Chen-Jihang/Mini-Monitor/04_Images/photograph/IMG_3699.JPG

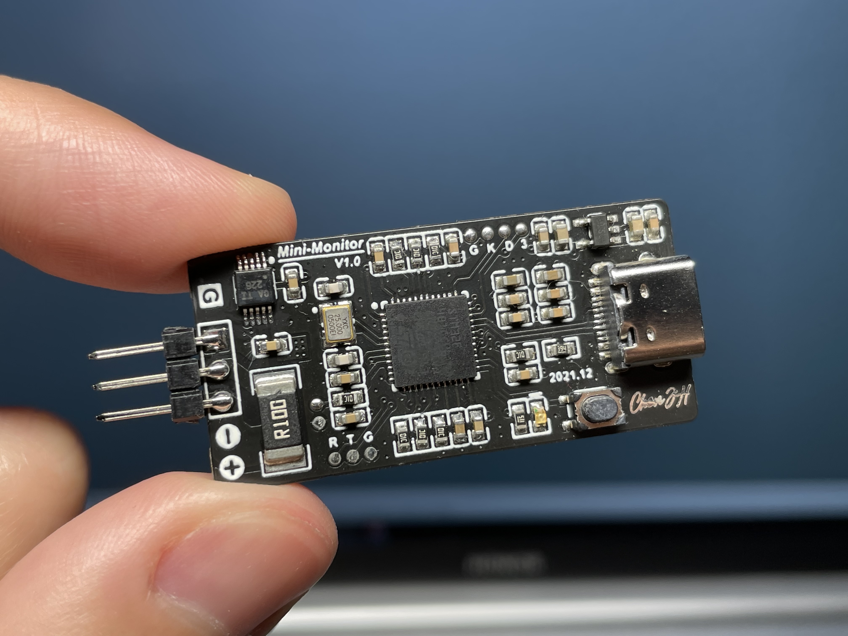
04_Images/photograph/IMG_3699.JPG
