Chen-Jihang/Mini-Monitor/04_Images/photograph/IMG_3701.JPG

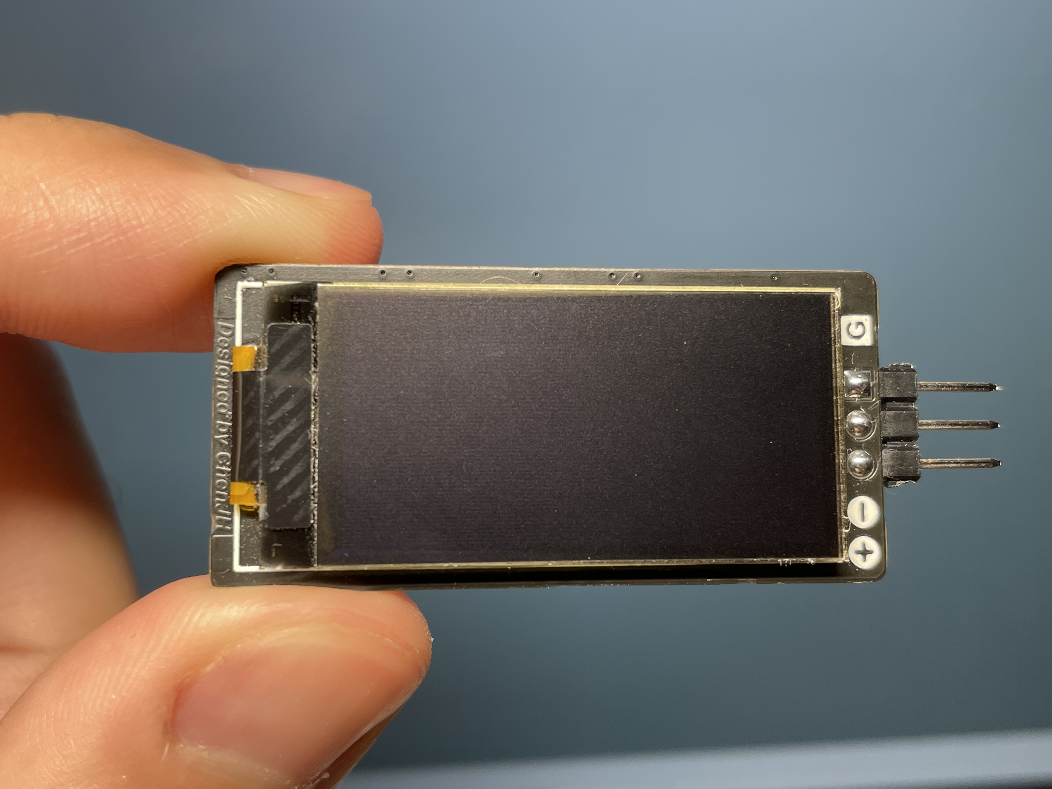
04_Images/photograph/IMG_3701.JPG
