Chen-Jihang/Mini-Monitor/04_Images/photograph/IMG_3709.JPG

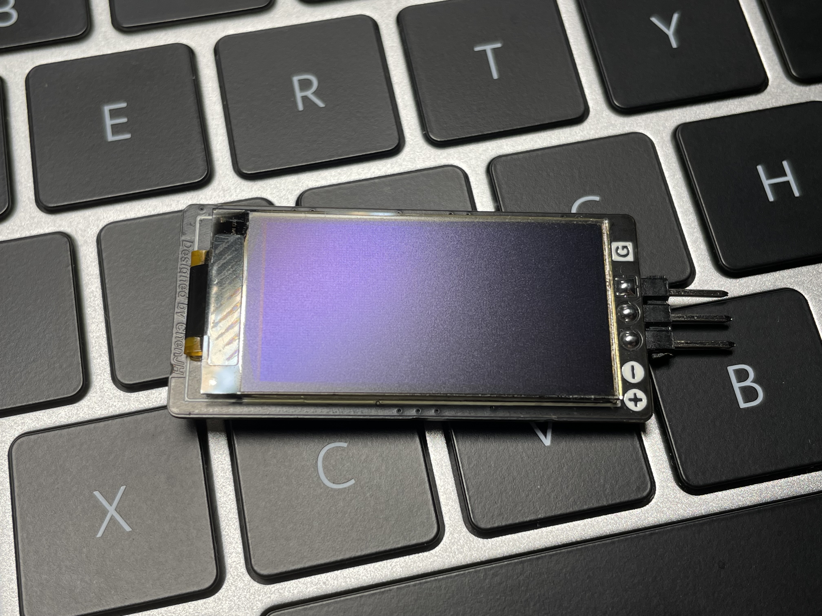
04_Images/photograph/IMG_3709.JPG
