Chen-Jihang/Mini-Monitor/04_Images/photograph/IMG_3772.JPG

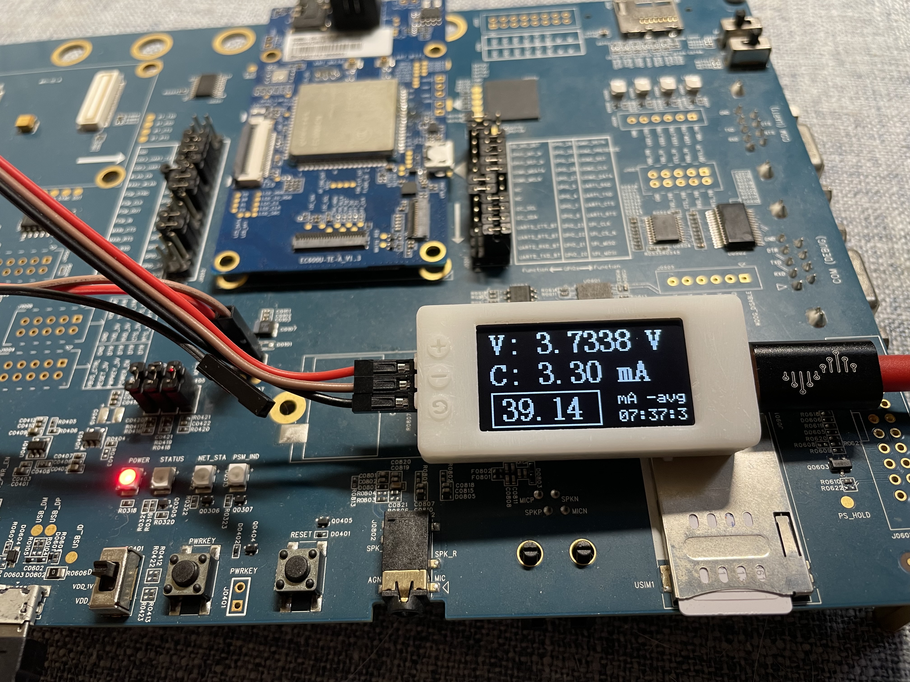
04_Images/photograph/IMG_3772.JPG
