Chen-Jihang/Mini-Monitor/04_Images/photograph/IMG_3781.JPG

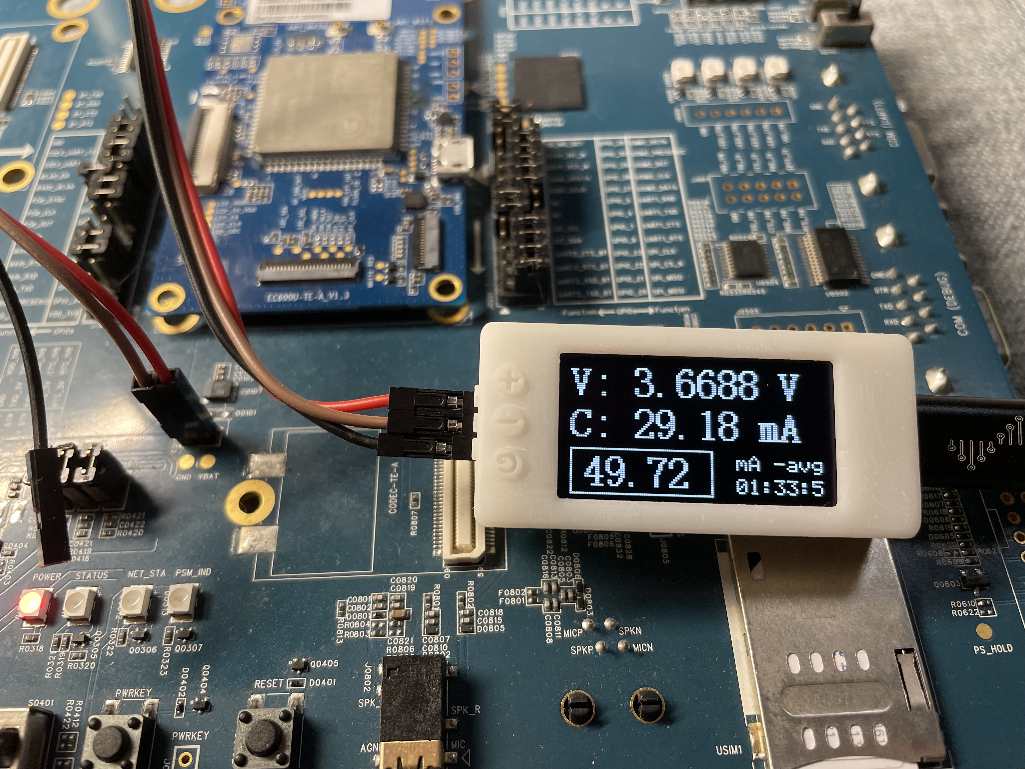
04_Images/photograph/IMG_3781.JPG
