Chen-Jihang/Mini-Monitor/04_Images/photograph/IMG_3813.JPG

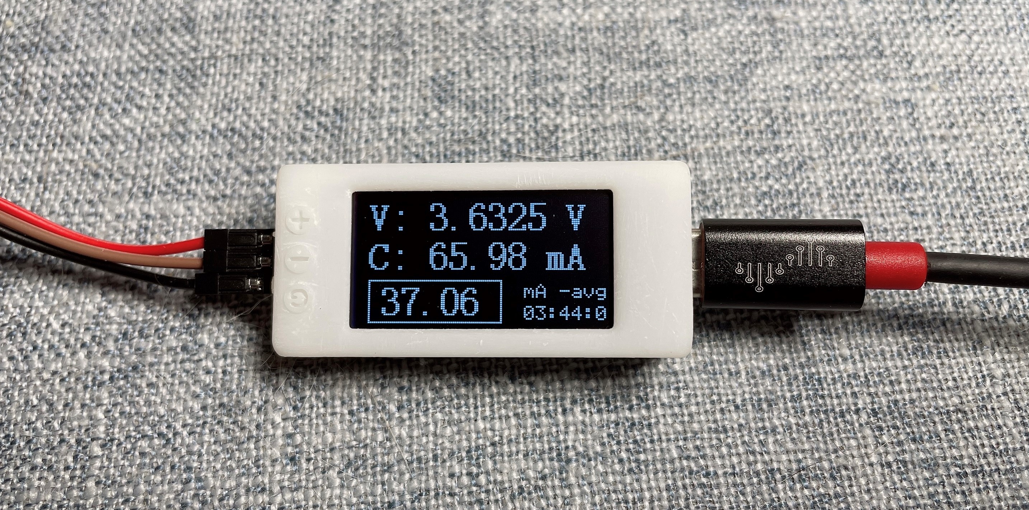
04_Images/photograph/IMG_3813.JPG
