Chen-Jihang/Mini-Monitor/04_Images/rendergraph/GEN_1.JPG

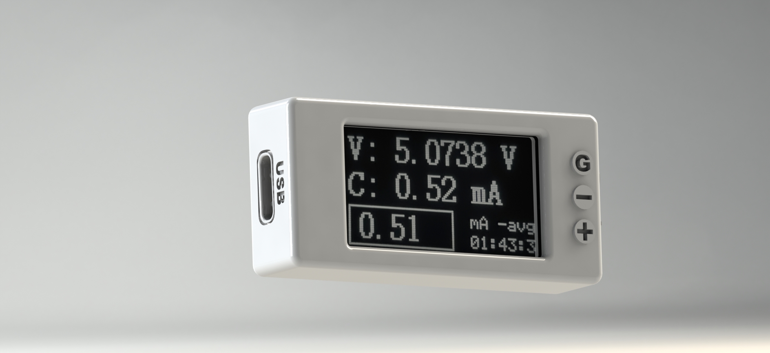
04_Images/rendergraph/GEN_1.JPG
