Chen-Jihang/Mini-Monitor/04_Images/rendergraph/GEN_3.JPG

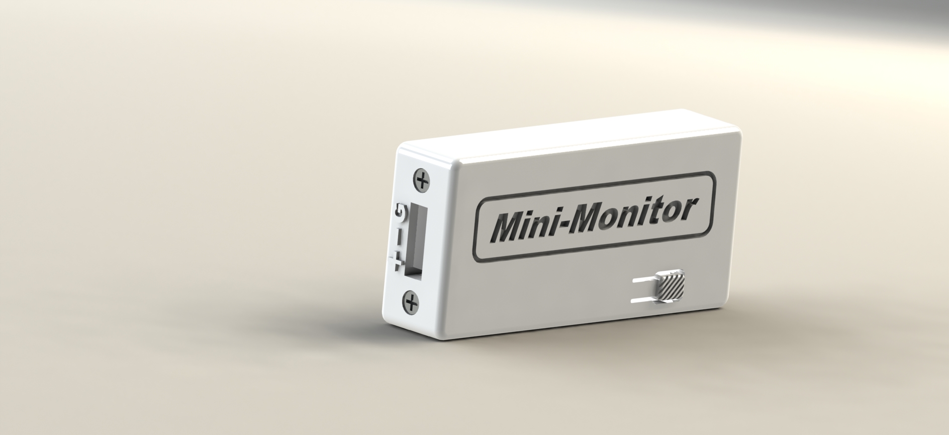
04_Images/rendergraph/GEN_3.JPG
