Chen-Jihang/Mini-Monitor/04_Images/rendergraph/GEN_6.JPG

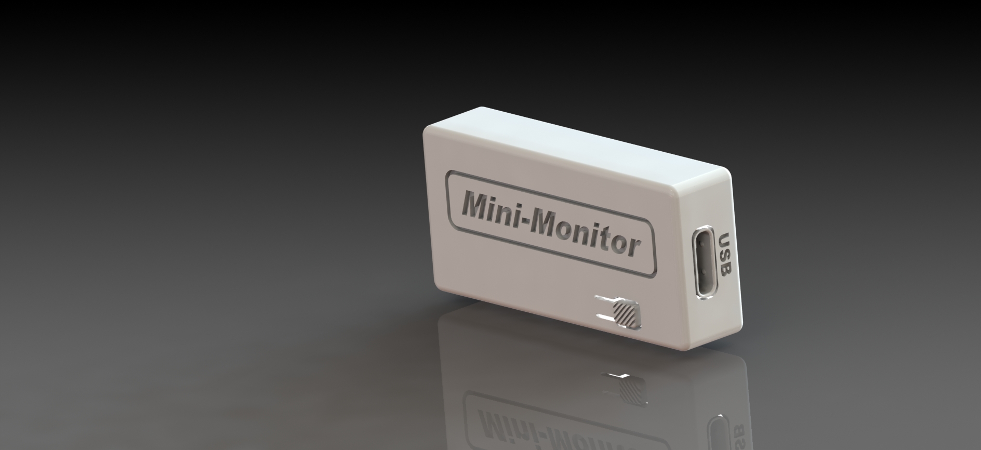
04_Images/rendergraph/GEN_6.JPG
