Chen-Jihang/Mini-Monitor/04_Images/rendergraph/GEN_9.JPG

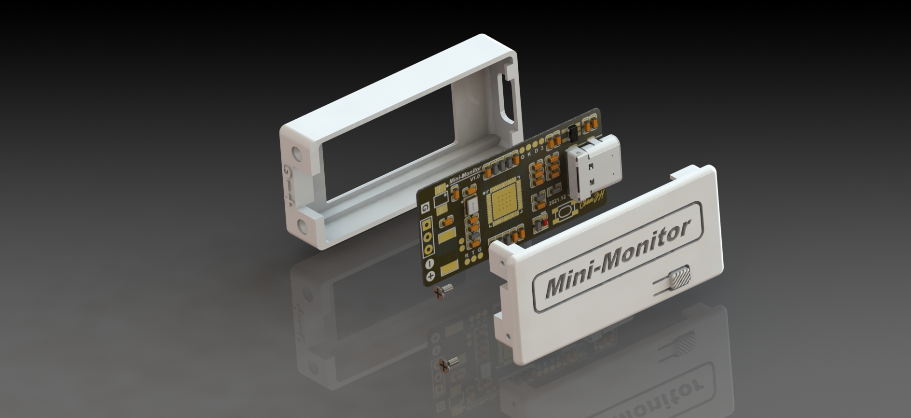
04_Images/rendergraph/GEN_9.JPG
