Chen-Jihang/Mini-Monitor/04_Images/rendergraph/GEN_11.JPG

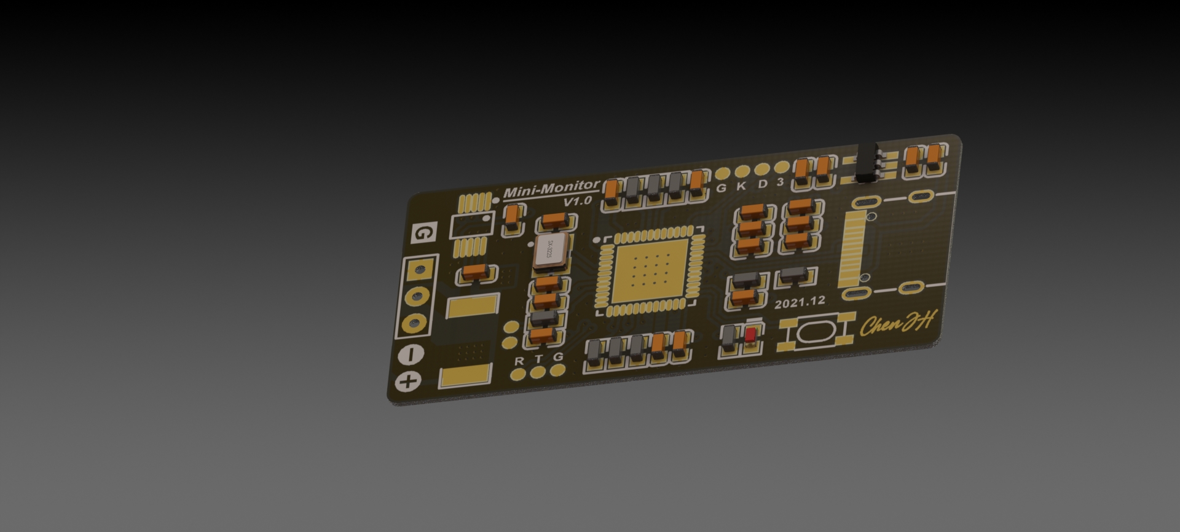
04_Images/rendergraph/GEN_11.JPG
