Chen-Jihang/Mini-Monitor/01_Software/Mini-Monitor__no_lvgl/HARDWARE/OLED/bmp.h

#ifndef __BMP_H
#define __BMP_H
//unsigned char BMP1[] =
//{
//	0x00,0x00,0x00,0x00,0x00,0x00,0x00,0x00,0x00,0x00,0x00,0x00,0x00,0x00,0x00,0x00,
//	0x00,0x00,0x00,0x00,0x00,0x00,0x00,0x00,0x00,0x00,0x00,0x00,0x00,0x00,0x00,0x00,
//	0x00,0x00,0x00,0x00,0x00,0x00,0x00,0x00,0x00,0x00,0x00,0x00,0x00,0x00,0x00,0x00,
//	0x00,0x00,0x00,0x00,0x00,0x00,0x00,0x00,0x00,0x00,0x00,0x00,0x00,0x00,0x00,0x00,
//	0x00,0x00,0x00,0x00,0x00,0x00,0x00,0x00,0x00,0x00,0x00,0x00,0x00,0x00,0x00,0x00,
//	0x00,0x00,0x00,0x00,0x00,0x00,0x00,0x00,0x00,0x00,0x00,0x00,0x00,0x00,0x00,0x00,
//	0x00,0x00,0x00,0x00,0x00,0x00,0x00,0x00,0x00,0x00,0x00,0x00,0x00,0x00,0x00,0x00,
//	0x00,0x00,0x00,0x00,0x00,0x00,0x00,0x00,0x00,0x00,0x00,0x00,0x00,0x00,0x00,0x00,
//	0x00,0x00,0x00,0x00,0x00,0x00,0x00,0x00,0x00,0x00,0x00,0x00,0x00,0xE0,0xE0,0x00,
//	0x00,0x00,0x80,0xE0,0xE0,0x00,0x00,0x00,0x80,0x80,0x80,0x00,0xC0,0xC0,0x80,0x00,
//	0x00,0x00,0xC0,0xC0,0xC0,0x00,0x80,0x80,0x80,0x00,0x00,0x00,0x00,0x00,0x00,0x00,
//	0x00,0x00,0x00,0x00,0x80,0xE0,0xE0,0x00,0x00,0x00,0x80,0xE0,0xE0,0x00,0x00,0x00,
//	0xC0,0xE0,0xE0,0xF0,0xF0,0xF0,0xE0,0xC0,0x00,0x00,0xE0,0xE0,0xC0,0x00,0x00,0x00,
//	0xE0,0xE0,0xE0,0x00,0x00,0xC0,0xC0,0xC0,0x00,0xE0,0xE0,0xE0,0xE0,0xE0,0xE0,0xE0,
//	0xE0,0xE0,0x00,0x80,0xC0,0xE0,0xF0,0x70,0x70,0xF0,0xE0,0xC0,0x00,0x00,0xC0,0xC0,
//	0xC0,0xC0,0xC0,0xC0,0xC0,0x80,0x00,0x00,0x00,0x00,0x00,0x00,0x00,0x00,0x00,0x00,
//	0x00,0x00,0x00,0x00,0x00,0x00,0x00,0x00,0x00,0x00,0x80,0xF0,0xFF,0xFF,0x3F,0xFF,
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
	0x00,0x00,0x00,0x00,0x00,0x0F,0x0F,0x0F,0x00,0x00,0x01,0x0F,0x0F,0x0F,0x01,0x00,
	0x00,0x0F,0x0F,0x0F,0x00,0x01,0x07,0x07,0x0F,0x0E,0x0E,0x0F,0x07,0x07,0x01,0x00,
	0x0F,0x0F,0x0F,0x00,0x00,0x00,0x0F,0x0F,0x0F,0x00,0x0F,0x0F,0x0F,0x00,0x00,0x07,
	0x0F,0x0F,0x0E,0x0E,0x00,0x01,0x07,0x07,0x0F,0x0E,0x0E,0x0F,0x07,0x07,0x01,0x00,
	0x0F,0x0F,0x0F,0x00,0x00,0x00,0x00,0x00,0x00,0x00,0x00,0x00,0x00,0x00,0x00,0x00,
	0x00,0x00,0x00,0x00,0x00,0x00,0x00,0x00,0x00,0x00,0x00,0x00,0x00,0x00,0x00,0x00,
	0x00,0x00,0x00,0x00,0x00,0x00,0x00,0x00,0x00,0x00,0x00,0x00,0x00,0x00,0x00,0x00,
	0x00,0x00,0x00,0x00,0x00,0x00,0x00,0x00,0x00,0x00,0x00,0x00,0x00,0x00,0x00,0x00,
	0x00,0x00,0x00,0x00,0x00,0x00,0x00,0x00,0x00,0x00,0x00,0x00,0x00,0x00,0x00,0x00,
	0x00,0x00,0x00,0x00,0x00,0x00,0x00,0x00,0x00,0x00,0x00,0x00,0x00,0x00,0x00,0x00,
	0x00,0x00,0x00,0x00,0x00,0x00,0x00,0x00,0x00,0x00,0x00,0x00,0x00,0x00,0x00,0x00,
	0x00,0x00,0x00,0x00,0x00,0x00,0x00,0x00,0x00,0x00,0x00,0x00,0x00,0x00,0x00,0x00,
	0x00,0x00,0x00,0x00,0x00,0x00,0x00,0x00,0x00,0x00,0x00,0x00,0x00,0x00,0x00,0x00,
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
};

#endif
