Chen-Jihang/Mini-Monitor/01_Software/Mini-Monitor__no_lvgl/HARDWARE/INA226/myiic.c

#include "myiic.h"
#include "delay.h"

//IIC初始化
void IIC_Init(void)
{
	GPIO_InitTypeDef GPIO_InitStruct = {0};

	/* GPIO Ports Clock Enable */
	__HAL_RCC_GPIOH_CLK_ENABLE();
	__HAL_RCC_GPIOB_CLK_ENABLE();

	/*Configure GPIO pin Output Level */
	HAL_GPIO_WritePin(GPIOB, GPIO_PIN_6|GPIO_PIN_7, GPIO_PIN_SET);

	/*Configure GPIO pins : PB6 PB7 */
	GPIO_InitStruct.Pin = GPIO_PIN_6|GPIO_PIN_7;
	GPIO_InitStruct.Mode = GPIO_MODE_OUTPUT_PP;
	GPIO_InitStruct.Pull = GPIO_PULLUP;
	GPIO_InitStruct.Speed = GPIO_SPEED_FREQ_VERY_HIGH;
	HAL_GPIO_Init(GPIOB, &GPIO_InitStruct);
    
	IIC_SDA=1;
	IIC_SCL=1; 

	delay_init(42); //42MHz
}

//产生IIC起始信号
void IIC_Start(void)
{
	SDA_OUT();     //sda线输出
	IIC_SDA=1;	  	  
	IIC_SCL=1;
	delay_us(DELAYUS*2);
 	IIC_SDA=0;//START:when CLK is high,DATA change form high to low 
	delay_us(DELAYUS*2);
	IIC_SCL=0;//钳住I2C总线，准备发送或接收数据 
	delay_us(DELAYUS*2);
}	  

//产生IIC停止信号
void IIC_Stop(void)
{
	SDA_OUT();//sda线输出
	IIC_SCL=0;
	IIC_SDA=0;//STOP:when CLK is high DATA change form low to high
 	delay_us(DELAYUS*2);
	IIC_SCL=1; 
	IIC_SDA=1;//发送I2C总线结束信号
	delay_us(DELAYUS*2);							   	
}

//等待应答信号到来
//返回值：1，接收应答失败
//        0，接收应答成功
u8 IIC_Wait_Ack(void)
{
	u8 ucErrTime=0;
	SDA_IN();      //SDA设置为输入  
	IIC_SDA=1;delay_us(DELAYUS);	   
	IIC_SCL=1;delay_us(DELAYUS);	 
	while(READ_SDA)
	{
		ucErrTime++;
		if(ucErrTime>250)
		{
			IIC_Stop();
			return 1;
		}
	}
	IIC_SCL=0;//时钟输出0 
	delay_us(DELAYUS);	   
	return 0;  
} 

//产生ACK应答
void IIC_Ack(void)
{
	IIC_SCL=0;
	SDA_OUT();
	IIC_SDA=0;
	delay_us(DELAYUS);
	IIC_SCL=1;
	delay_us(DELAYUS);
	IIC_SCL=0;
}

//不产生ACK应答		    
void IIC_NAck(void)
{
	IIC_SCL=0;
	SDA_OUT();
	IIC_SDA=1;
	delay_us(DELAYUS);
	IIC_SCL=1;
	delay_us(DELAYUS);
	IIC_SCL=0;
}	

//IIC发送一个字节
//返回从机有无应答
//1，有应答
//0，无应答			  
void IIC_Send_Byte(u8 txd)
{                        
	u8 t;   
	SDA_OUT(); 	    
	IIC_SCL=0;//拉低时钟开始数据传输
	for(t=0;t<8;t++)
	{              
		IIC_SDA=(txd&0x80)>>7;
		txd<<=1; 	  
//		delay_us(DELAYUS);
		IIC_SCL=1;
		delay_us(DELAYUS); 
		IIC_SCL=0;	
		delay_us(DELAYUS);
	}	 
} 	    

//读1个字节，ack=1时，发送ACK，ack=0，发送nACK   
u8 IIC_Read_Byte(unsigned char ack)
{
	unsigned char i,receive=0;
	SDA_IN();//SDA设置为输入
	for(i=0;i<8;i++ )
	{
		IIC_SCL=0; 
		delay_us(DELAYUS);
		IIC_SCL=1;
		receive<<=1;
		if(READ_SDA)receive++;   
		delay_us(DELAYUS); 
	}					 
	if (!ack)
		IIC_NAck();//发送nACK
	else
		IIC_Ack(); //发送ACK   
	return receive;
}
